PapaKarlo787/ozcomp/docs/ATmega8 + PCD8544_ работа с графическим дисплеем от телефонов Nokia 5110_3310_files/03.png

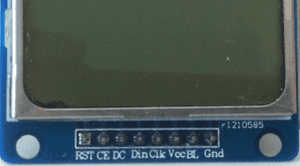
docs/ATmega8 + PCD8544_ работа с графическим дисплеем от телефонов Nokia 5110_3310_files/03.png
