PapaKarlo787/ozcomp/docs/ATmega8 + PCD8544_ работа с графическим дисплеем от телефонов Nokia 5110_3310_files/05.jpg

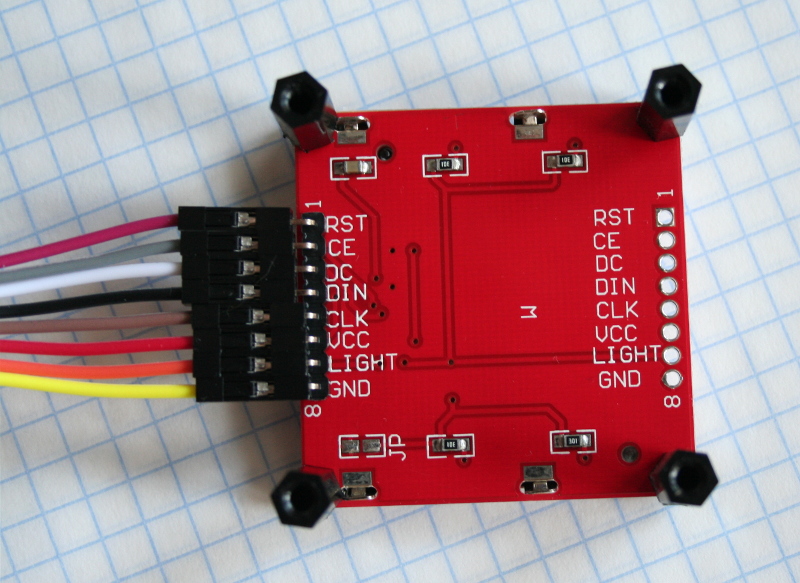
docs/ATmega8 + PCD8544_ работа с графическим дисплеем от телефонов Nokia 5110_3310_files/05.jpg
