PapaKarlo787/ozcomp/arch/int_ariphmetics.h

void add_rr() {
	readRegisters();
	setFlags(R[r1] += R[r2]);
}

void add_rc() {
	readRegisters();
	setFlags(R[r1] += readNum());
}

void sub_rr() {
	readRegisters();
	setFlags(R[r1] -= R[r2]);
}

void sub_rc() {
	readRegisters();
	setFlags(R[r1] -= readNum());
}

void mul_rr() {
	readRegisters();
	setFlags(R[r1] *= R[r2]);
}

void mul_rc() {
	readRegisters();
	setFlags(R[r1] *= readNum());
}

void div_rr() {
	readRegisters();
	setFlags(R[r1] /= R[r2]);
}

void div_rc() {
	readRegisters();
	setFlags(R[r1] /= readNum());
}

void pow_rr() {
	readRegisters();
	R[r1] = pow(R[r1], R[r2]);
}

void pow_rc() {
	readRegisters();
	R[r1] = pow(R[r1], readNum());
}

void cmp_rr() {
	readRegisters();
	setFlags(R[r1] - R[r2]);
}

void cmp_rc() {
	readRegisters();
	setFlags(R[r1] - readNum());
}

void mod_rr() {
	readRegisters();
	setFlags(R[r1] %= R[r2]);
}

void mod_rc() {
	readRegisters();
	setFlags(R[r1] %= readNum());
}

void test() {
	readRegisters();
	setFlags(R[r1]);
}
